solmorth/YetAnotherTNC/src/gps.c

#include "gps.h"
#include <string.h>
#include <zephyr/device.h>
#include <zephyr/drivers/gpio.h>
#include <zephyr/drivers/uart.h>
#include <zephyr/sys/printk.h>
#include <zephyr/sys/ring_buffer.h>
#include "ax25.h"
#include "gps_format.h"
#include "mode_select.h"
#include "tnc.h"
#include "tnc_config.h"
#include "log_ts.h"

#define GPS_ENABLE_PIN_NODE DT_NODELABEL(gps_enable_pin)
#define GPS_UART_NODE DT_NODELABEL(uart1)

#if DT_NODE_EXISTS(GPS_ENABLE_PIN_NODE)
static const struct gpio_dt_spec gps_enable_spec = GPIO_DT_SPEC_GET(GPS_ENABLE_PIN_NODE, gpios);
#endif

static const struct device *const gps_uart_dev = DEVICE_DT_GET(GPS_UART_NODE);

static bool gps_enabled = false;

/* NMEA sentences arrive as short CRLF-terminated lines at a few Hz. Batch-
 * drain them on a short idle timer rather than printk-ing from the ISR:
 * printk() over USB CDC ACM can block indefinitely if called from interrupt
 * context, which freezes the whole system (same hazard as uart_isr() in
 * main.c).
 */
#define GPS_RX_RING_BUF_SIZE 256
#define GPS_RX_IDLE_TIMEOUT_MS 50

RING_BUF_DECLARE(gps_rx_ring_buf, GPS_RX_RING_BUF_SIZE);

static bool gps_has_fix;
static bool gps_has_position;
static char gps_lat[9];
static char gps_lon[10];

/* Beacon sent at the configured interval while a fix is held. Callsign and
 * interval come from tnc_config (runtime-settable via KISS_CMD_SETHARDWARE,
 * persisted across reboots); lat/lon from the most recent GGA sentence.
 */
static void gps_beacon_work_handler(struct k_work *work);
static K_WORK_DELAYABLE_DEFINE(gps_beacon_work, gps_beacon_work_handler);

static void gps_beacon_work_handler(struct k_work *work)
{
	ARG_UNUSED(work);

	char lat[9];
	char lon[10];

	if (tnc_config_get_fixed_pos_enabled()) {
		/* Fixed position mode never has GPS running to kick this work
		 * item back alive (see gps_start_fixed_position_beacon), so
		 * it must always reschedule itself below, unlike the
		 * live-GPS path which relies on gps_process_nmea_line to
		 * restart it on fix acquisition.
		 */
		if (!tnc_config_get_fixed_pos_configured()) {
			k_work_reschedule(&gps_beacon_work,
					   K_SECONDS(tnc_config_get_beacon_interval_s()));
			return;
		}
		gps_format_encode_position(tnc_config_get_fixed_lat(), tnc_config_get_fixed_lon(),
					    lat, lon);
	} else {
		if (!gps_has_fix) {
			return;
		}

		/* fix_quality can flip true on a GGA line whose lat/lon fields are
		 * still parseable garbage in some receivers' first fixed sentence -
		 * don't transmit a position until gps_process_nmea_line has actually
		 * captured one.
		 */
		if (!gps_has_position) {
			k_work_reschedule(&gps_beacon_work,
					   K_SECONDS(tnc_config_get_beacon_interval_s()));
			return;
		}
		memcpy(lat, gps_lat, sizeof(lat));
		memcpy(lon, gps_lon, sizeof(lon));
	}

	ax25_frame_t frame = {0};

	frame.src = *tnc_config_get_callsign();
	ax25_parse_callsign("APRS", &frame.dest);
	frame.control = AX25_CTRL_UI;
	frame.pid = AX25_PID_NO_L3;

	frame.payload_len = gps_format_build_position_payload(
		lat, lon, tnc_config_get_comment(), frame.payload, sizeof(frame.payload));

	if (frame.payload_len == 0) {
		k_work_reschedule(&gps_beacon_work,
				   K_SECONDS(tnc_config_get_beacon_interval_s()));
		return;
	}

	uint8_t tx_buf[AX25_MAX_FRAME_LEN];
	int tx_len = ax25_encode(&frame, tx_buf, sizeof(tx_buf));

	if (tx_len > 0) {
		printk("[GPS] %s, sending %d-byte position beacon\n",
		       tnc_config_get_fixed_pos_enabled() ? "Fixed position" : "Fix held", tx_len);
		tnc_queue_tx_packet(tx_buf, (size_t)tx_len, APP_MODE_STANDALONE);
	}

	k_work_reschedule(&gps_beacon_work, K_SECONDS(tnc_config_get_beacon_interval_s()));
}

/* $GPGGA/$GNGGA,time,lat,NS,lon,EW,fix_quality,... - fix_quality (the field
 * after the 6th comma) is 0 when no fix is held, non-zero otherwise.
 */
static void gps_process_nmea_line(const char *line)
{
	printk("[GPS] %s\n", line);

	if (strncmp(line, "$GPGGA", 6) != 0 && strncmp(line, "$GNGGA", 6) != 0) {
		return;
	}

	/* Refresh the last-known position on every GGA line, not just fix
	 * transitions, so the beacon reflects current position while moving.
	 */
	char lat[9];
	char lon[10];
	if (gps_format_parse_gga_position(line, lat, lon)) {
		memcpy(gps_lat, lat, sizeof(gps_lat));
		memcpy(gps_lon, lon, sizeof(gps_lon));
		gps_has_position = true;
	}

	const char *field = line;
	for (int i = 0; i < 6 && field != NULL; i++) {
		field = strchr(field + 1, ',');
	}

	bool fix = (field != NULL && field[1] != '0' && field[1] != ',');

	if (fix == gps_has_fix) {
		return;
	}

	gps_has_fix = fix;
	printk("[GPS] Fix %s\n", fix ? "ACQUIRED" : "LOST");
	if (fix) {
		k_work_reschedule(&gps_beacon_work, K_NO_WAIT);
	}
}

#define GPS_NMEA_LINE_MAX 96
static char gps_line_buf[GPS_NMEA_LINE_MAX];
static size_t gps_line_len;

static void gps_rx_work_handler(struct k_work *work)
{
	ARG_UNUSED(work);

	uint8_t buf[GPS_RX_RING_BUF_SIZE];
	uint32_t len = ring_buf_get(&gps_rx_ring_buf, buf, sizeof(buf));

	for (uint32_t i = 0; i < len; i++) {
		char c = (char)buf[i];

		if (c == '\n' || c == '\r') {
			if (gps_line_len > 0) {
				gps_line_buf[gps_line_len] = '\0';
				gps_process_nmea_line(gps_line_buf);
				gps_line_len = 0;
			}
			continue;
		}

		if (gps_line_len < GPS_NMEA_LINE_MAX - 1) {
			gps_line_buf[gps_line_len++] = c;
		} else {
			/* Overlong/garbled sentence - drop it and resync on the next line. */
			gps_line_len = 0;
		}
	}
}
static K_WORK_DELAYABLE_DEFINE(gps_rx_work, gps_rx_work_handler);

static void gps_uart_isr(const struct device *dev, void *user_data)
{
	ARG_UNUSED(user_data);

	uart_irq_update(dev);

	if (uart_irq_rx_ready(dev)) {
		uint8_t buf[32];
		int len;

		while ((len = uart_fifo_read(dev, buf, sizeof(buf))) > 0) {
			ring_buf_put(&gps_rx_ring_buf, buf, len);
		}

		k_work_reschedule(&gps_rx_work, K_MSEC(GPS_RX_IDLE_TIMEOUT_MS));
	}
}

int gps_init(void)
{
	int ret = 0;

	if (mode_select_get_current() != APP_MODE_STANDALONE) {
		printk("GPS init skipped: not in standalone mode\n");
		return 0;
	}

#if DT_NODE_EXISTS(GPS_ENABLE_PIN_NODE)
	if (gpio_is_ready_dt(&gps_enable_spec)) {
		ret = gpio_pin_configure_dt(&gps_enable_spec, GPIO_OUTPUT_INACTIVE);
		if (ret < 0) {
			printk("Failed to configure GPS enable pin: %d\n", ret);
			return ret;
		}
		printk("GPS Enable Pin (Pin %d) initialized (default LOW / disabled)\n",
		       gps_enable_spec.pin);
	} else {
		printk("Warning: GPS enable GPIO device not ready\n");
	}
#else
	printk("Warning: gps_enable_pin DT node not defined\n");
#endif

	if (!device_is_ready(gps_uart_dev)) {
		printk("Warning: GPS UART (uart1) device not ready\n");
	} else {
		printk("GPS UART (uart1) ready\n");

		int uart_ret = uart_irq_callback_user_data_set(gps_uart_dev, gps_uart_isr, NULL);
		if (uart_ret < 0) {
			printk("Warning: GPS UART interrupt-driven API not supported: %d\n",
			       uart_ret);
		} else {
			uart_irq_rx_enable(gps_uart_dev);
		}
	}

	gps_enabled = false;
	return ret;
}

void gps_enable_set(bool enable)
{
#if DT_NODE_EXISTS(GPS_ENABLE_PIN_NODE)
	if (gpio_is_ready_dt(&gps_enable_spec)) {
		gpio_pin_set_dt(&gps_enable_spec, enable ? 1 : 0);
		gps_enabled = enable;
		printk("[GPS] Enable pin set to: %s\n", enable ? "HIGH (enabled)" : "LOW (disabled)");
	}
#endif
}

bool gps_is_enabled(void)
{
	return gps_enabled;
}

void gps_start_fixed_position_beacon(void)
{
	printk("[GPS] Fixed position mode: GPS hardware not initialized, beaconing stored position\n");
	k_work_reschedule(&gps_beacon_work, K_NO_WAIT);
}
